Riley903/VP400KH-10-Pack-Battery-Monitor/NiCd Battery Shield - VP400KH/Charging Dummy Board/3D Models/Molex-2Pos-RA.stp

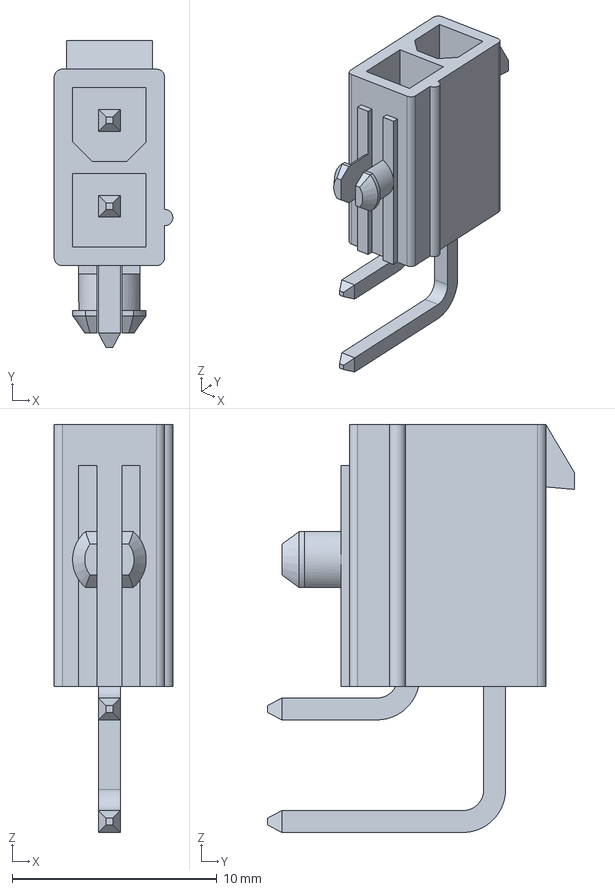
[picture p15: CAD file, 2021-07-20]
NiCd Battery Shield - VP400KH/Charging Dummy Board/3D Models/Molex-2Pos-RA.stp
5.80 x 15.0 x 19.9 mm
