Riley903/VP400KH-10-Pack-Battery-Monitor/NiCd Battery Shield - VP400KH/NiCd Battery Shield - VP400KH-REV 1.1/3D Models/keystone-PN7795.STEP

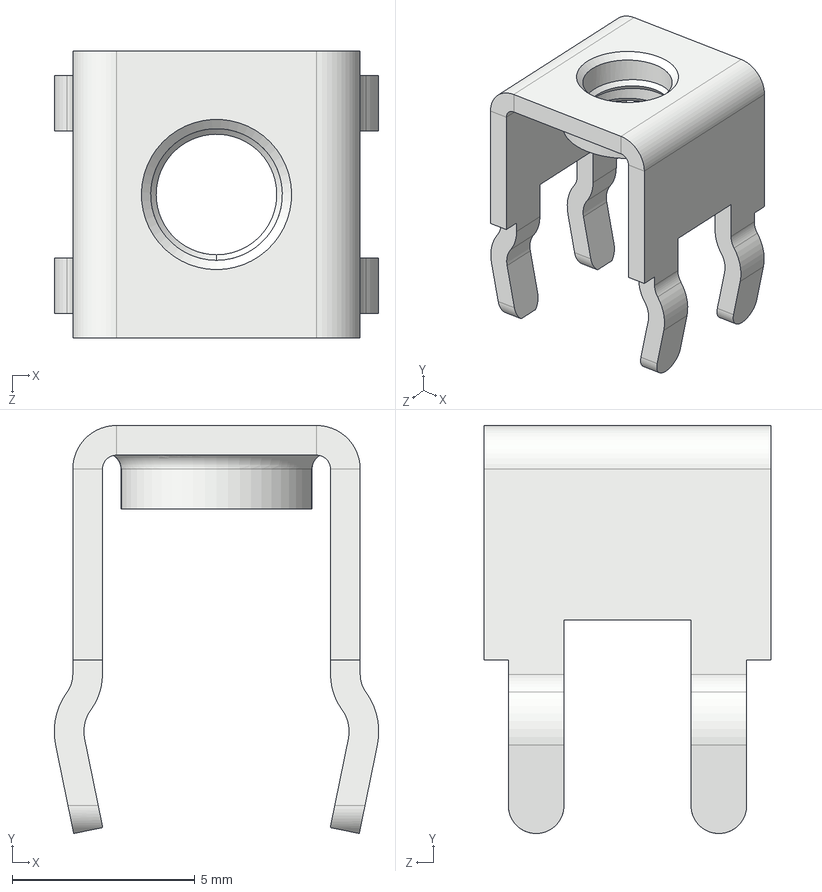
[picture p16: CAD file, 2021-07-20]
NiCd Battery Shield - VP400KH/NiCd Battery Shield - VP400KH-REV 1.1/3D Models/keystone-PN7795.STEP
8.89 x 11.2 x 7.87 mm
