Riley903/VP400KH-10-Pack-Battery-Monitor/NiCd Battery Tester Rev 3/3D Models/CUI_DEVICES_TB005-762-02BE.step

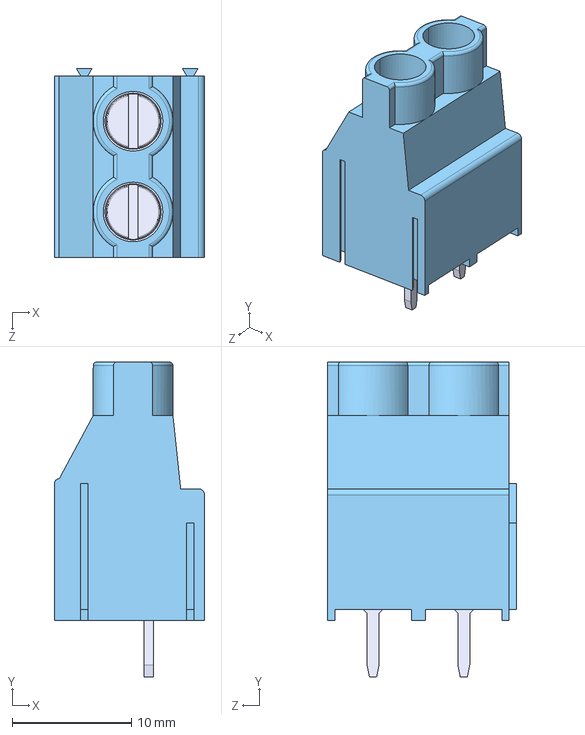
[picture p17: CAD file, 2021-07-20]
NiCd Battery Tester Rev 3/3D Models/CUI_DEVICES_TB005-762-02BE.step
12.6 x 26.5 x 15.8 mm
